mangaorphy/alertreck/docs/figures/chapter5/fig_5_0_training_curves.png

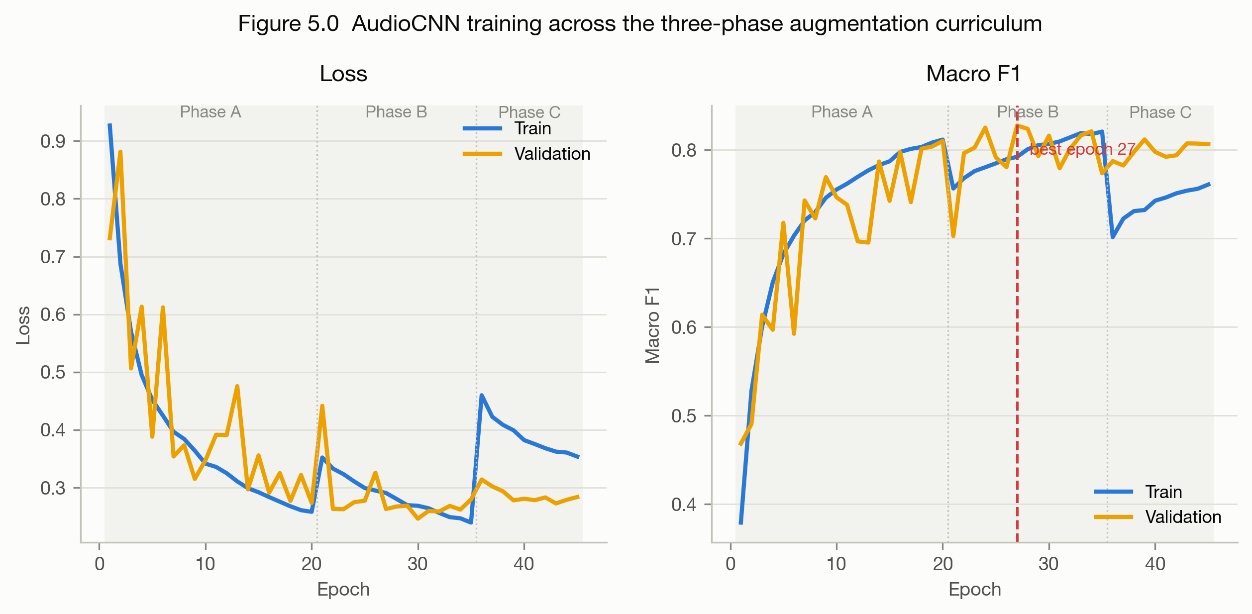
docs/figures/chapter5/fig_5_0_training_curves.png
