mangaorphy/alertreck/docs/figures/chapter5/fig_5_2_per_class_f1.png

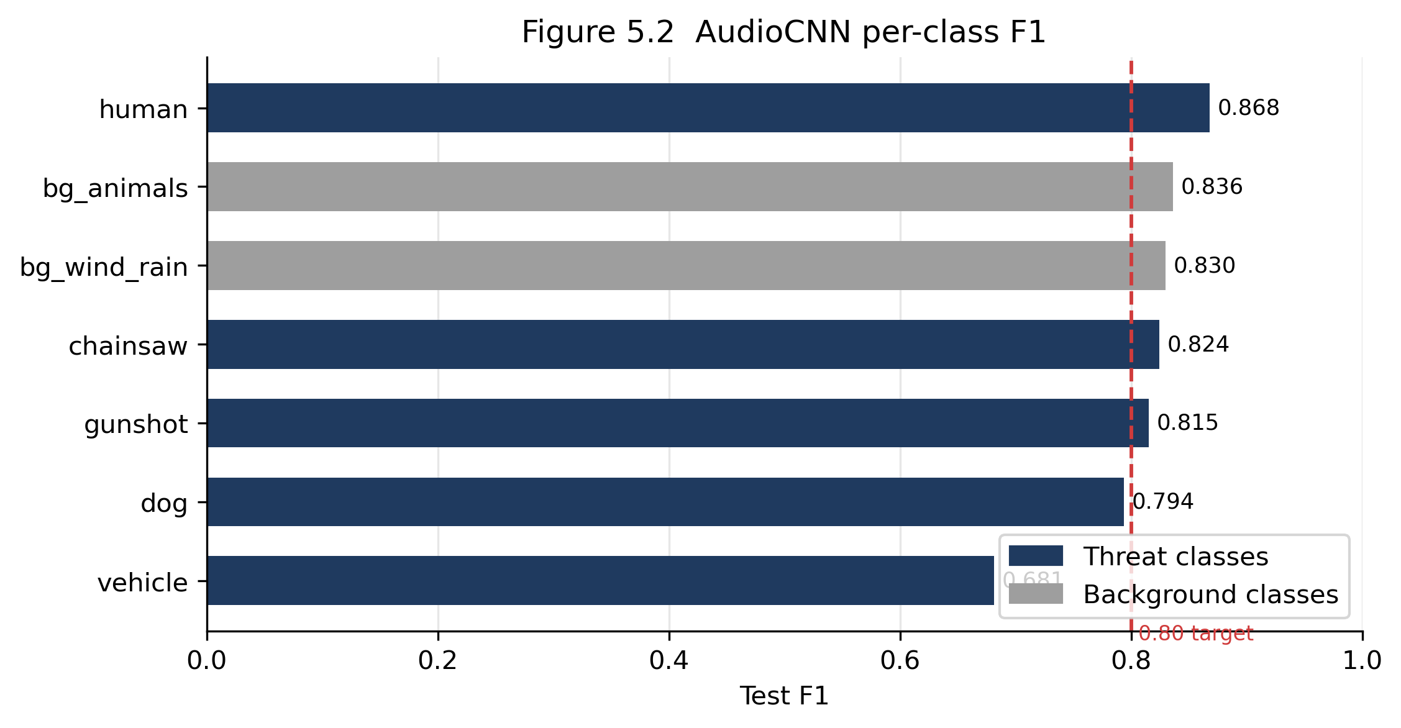
docs/figures/chapter5/fig_5_2_per_class_f1.png
