mangaorphy/alertreck/docs/figures/chapter5/fig_5_3_f1_vs_auc.png

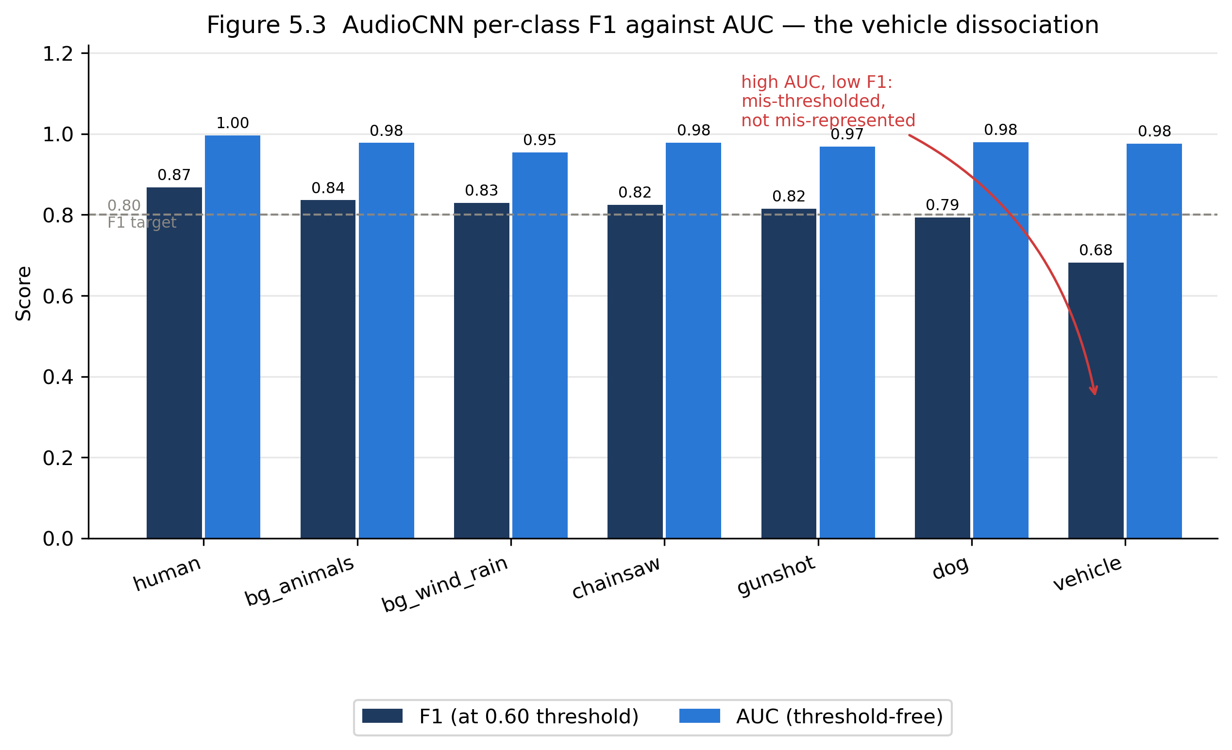
docs/figures/chapter5/fig_5_3_f1_vs_auc.png
