mangaorphy/alertreck/docs/figures/chapter5/fig_5_4_volume_vs_f1.png

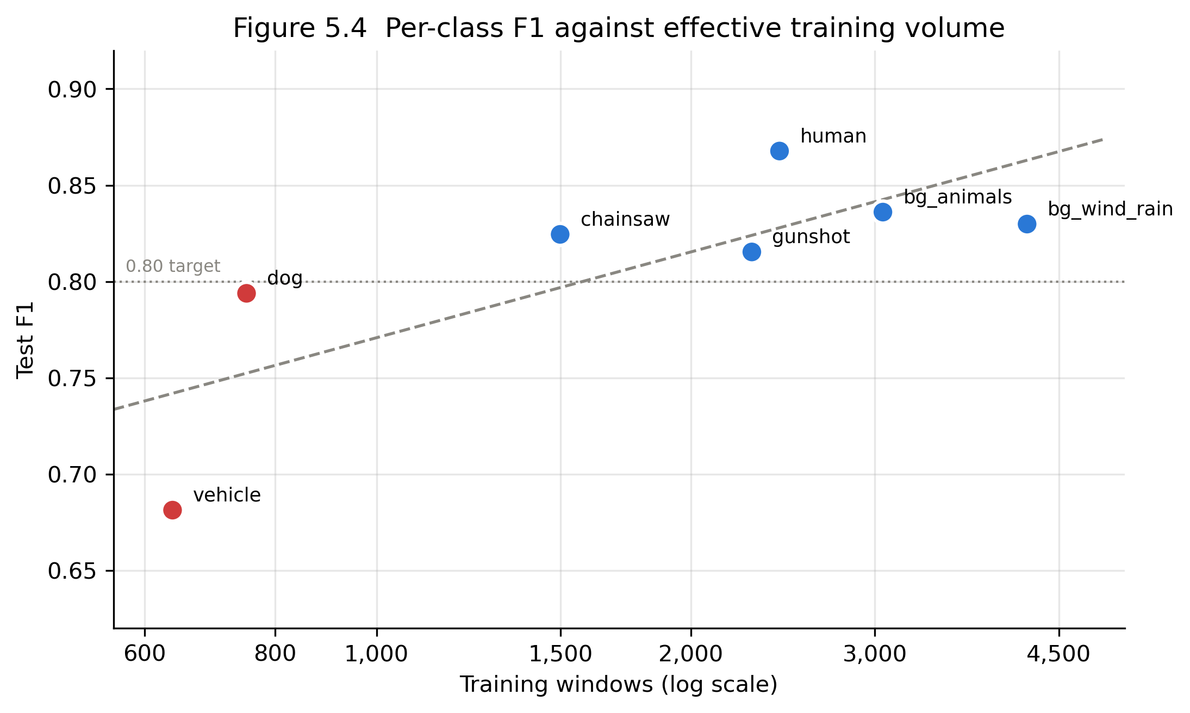
docs/figures/chapter5/fig_5_4_volume_vs_f1.png
