mangaorphy/alertreck/docs/figures/chapter5/fig_5_5_cross_model_f1.png

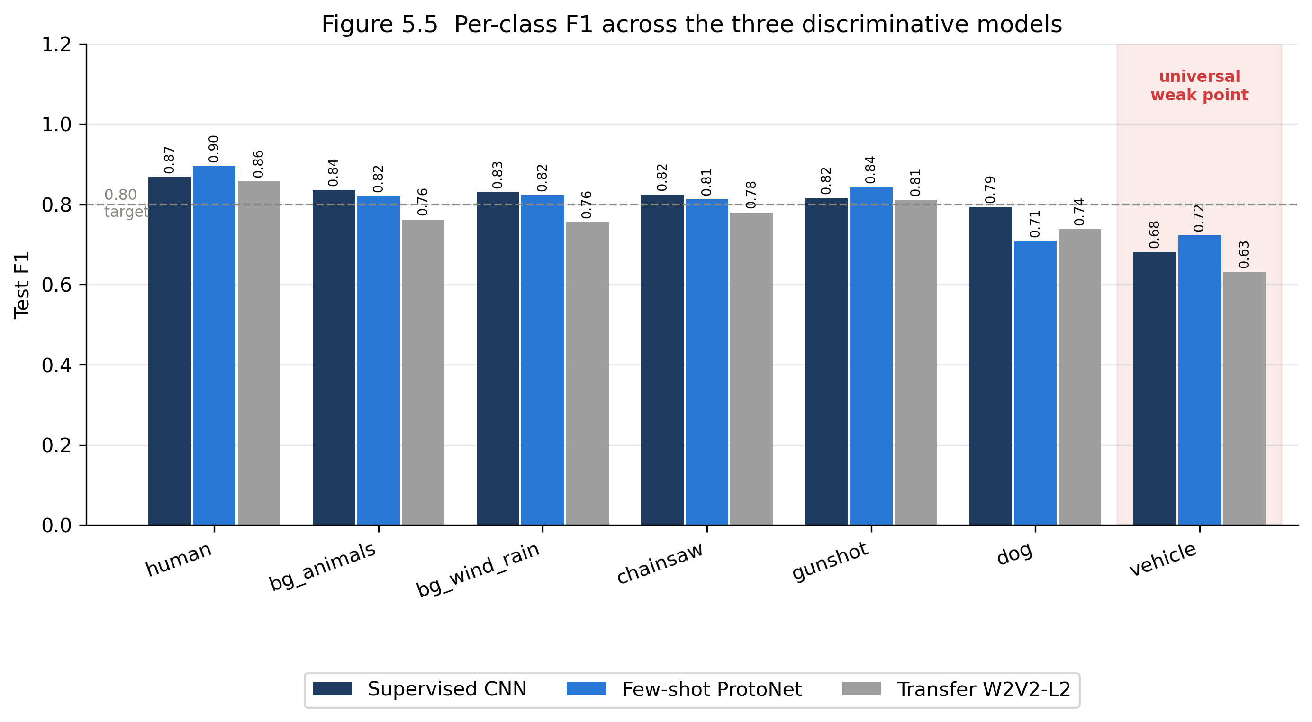
docs/figures/chapter5/fig_5_5_cross_model_f1.png
