mangaorphy/alertreck/docs/figures/chapter5/fig_5_6_anomaly_auc.png

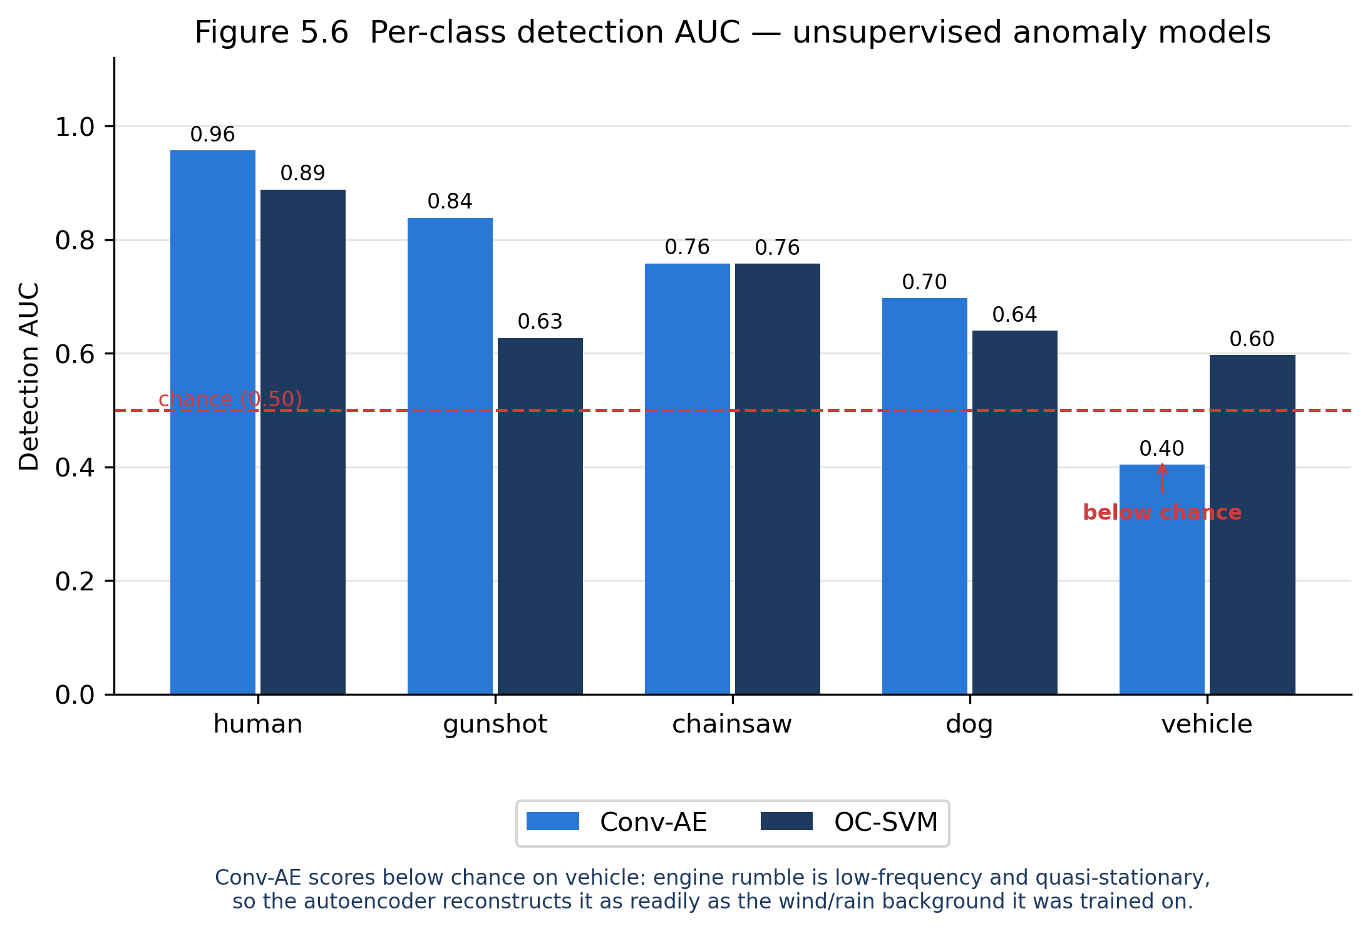
docs/figures/chapter5/fig_5_6_anomaly_auc.png
