mangaorphy/alertreck/docs/figures/chapter5/fig_5_7_confusion_matrix.png

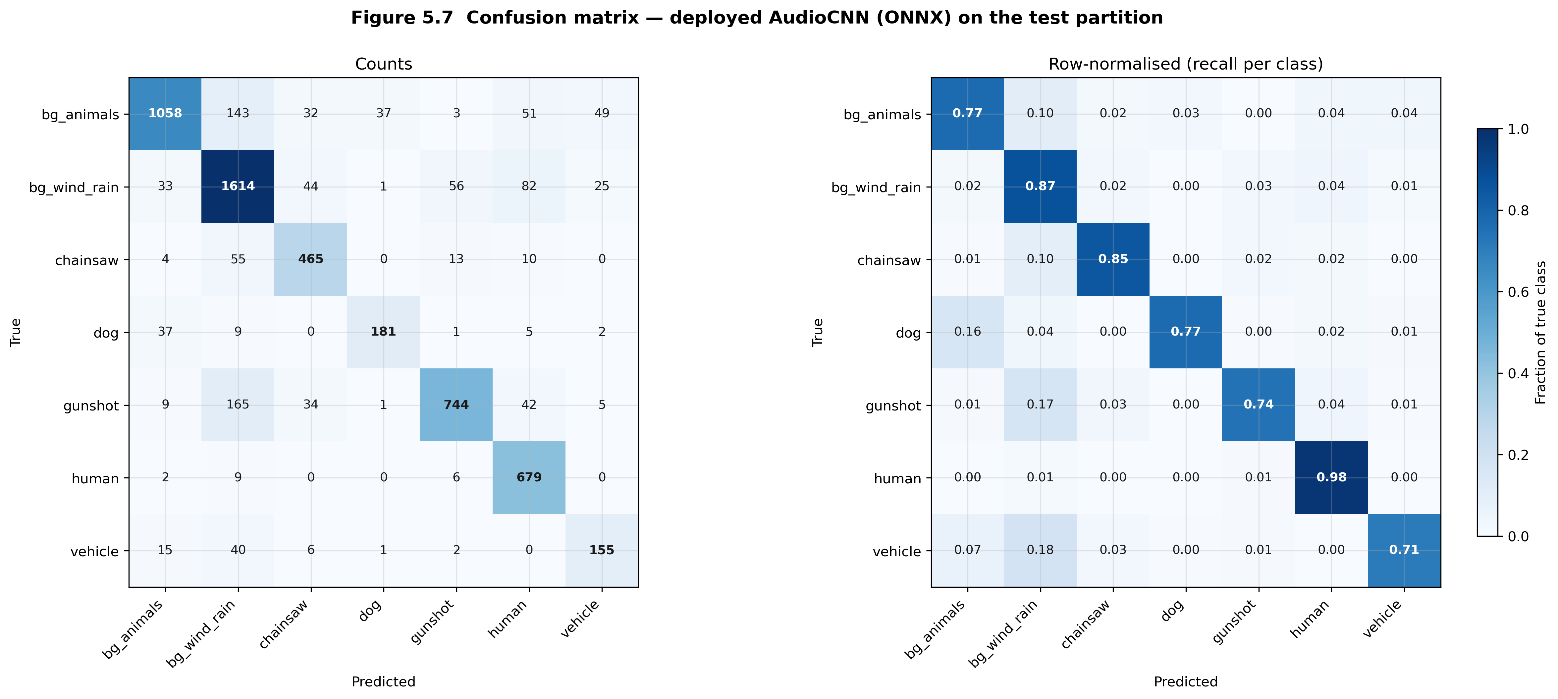
docs/figures/chapter5/fig_5_7_confusion_matrix.png
