mangaorphy/alertreck/docs/figures/feature_samples/0_background_animals.png

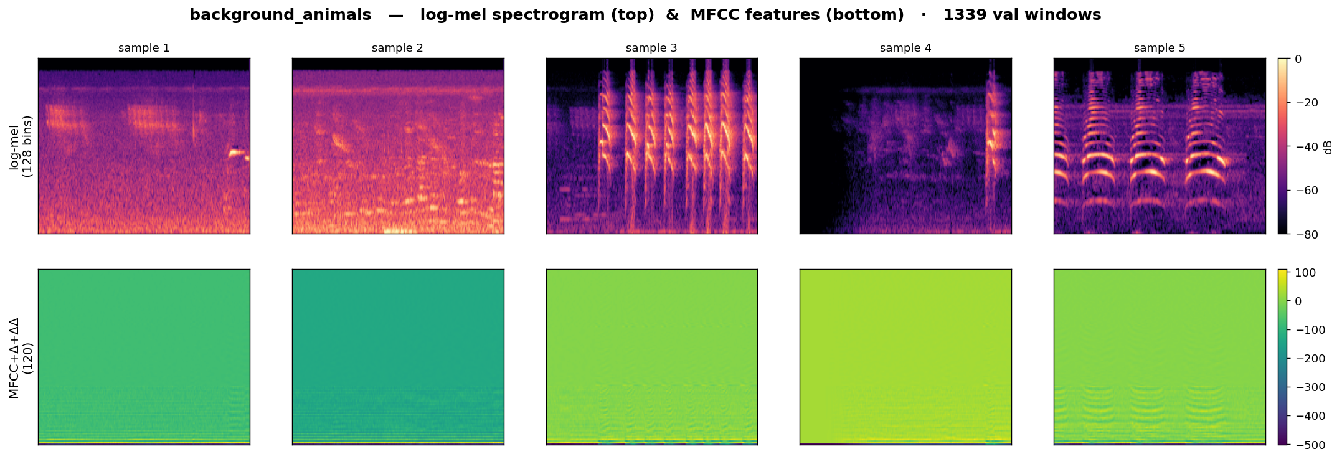
docs/figures/feature_samples/0_background_animals.png
