mangaorphy/alertreck/docs/figures/feature_samples/1_background_wind_rain.png

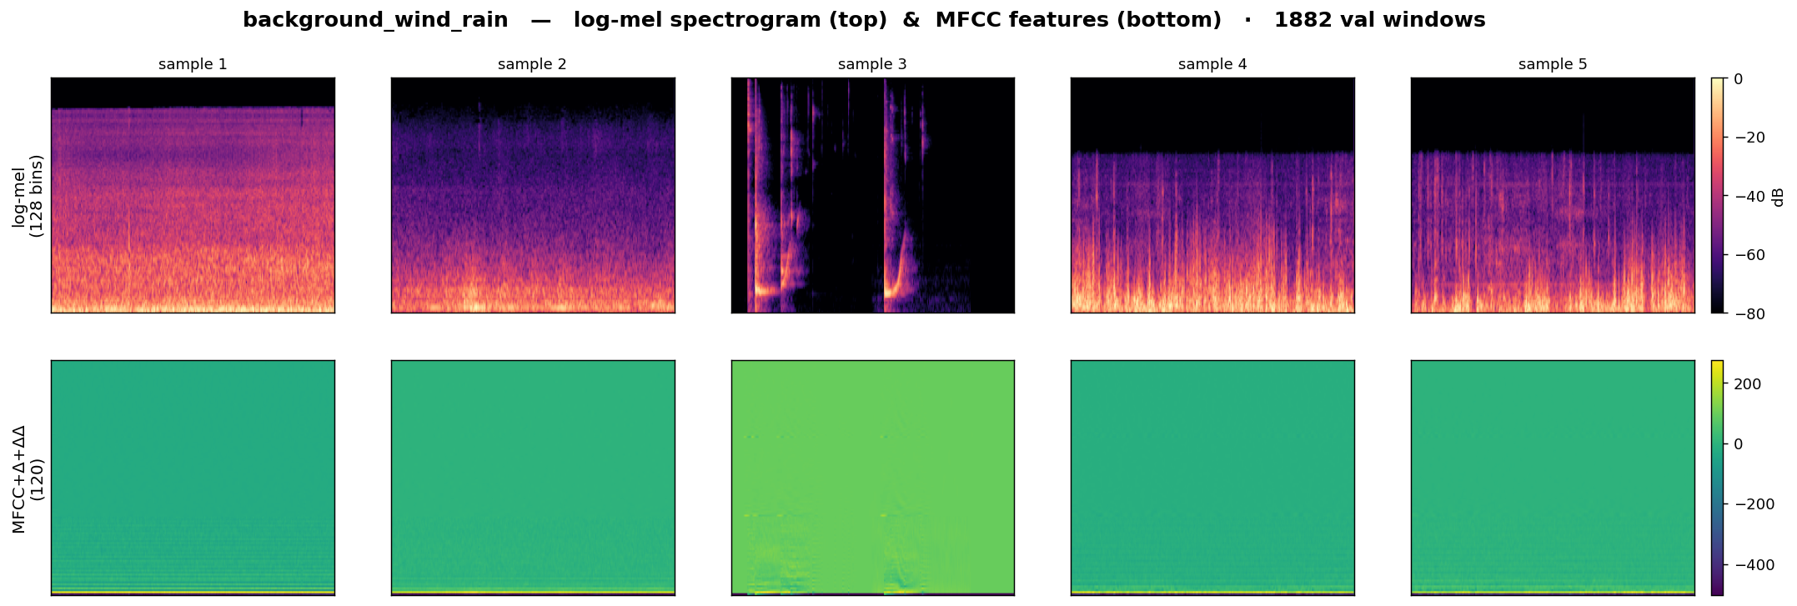
docs/figures/feature_samples/1_background_wind_rain.png
