mangaorphy/alertreck/docs/figures/feature_samples/2_threat_chainsaw.png

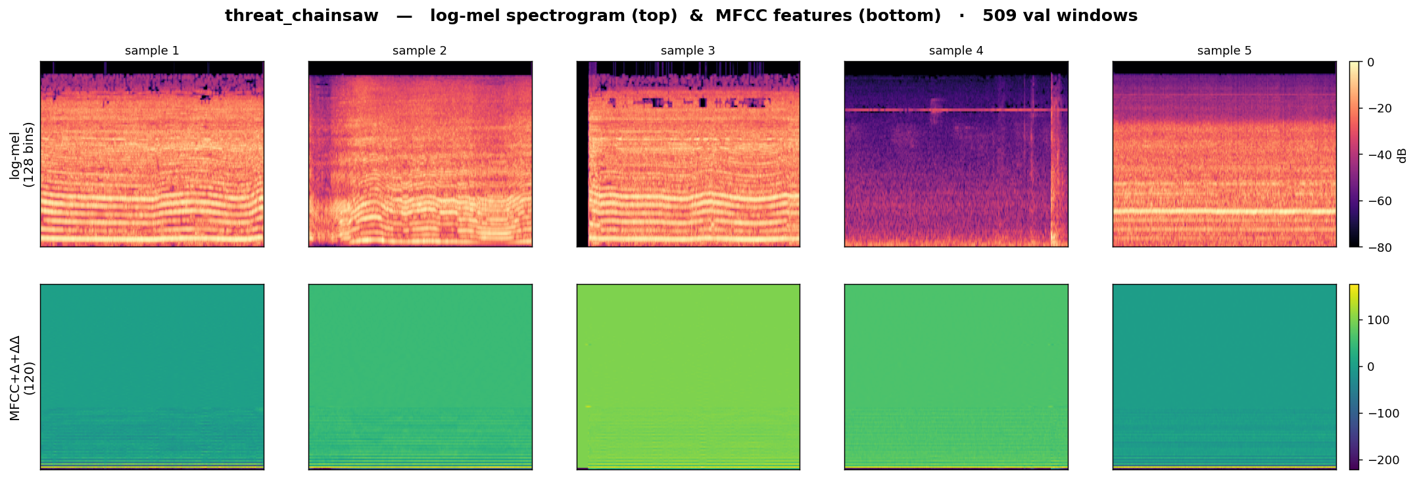
docs/figures/feature_samples/2_threat_chainsaw.png
