mangaorphy/alertreck/docs/figures/feature_samples/4_threat_gunshot.png

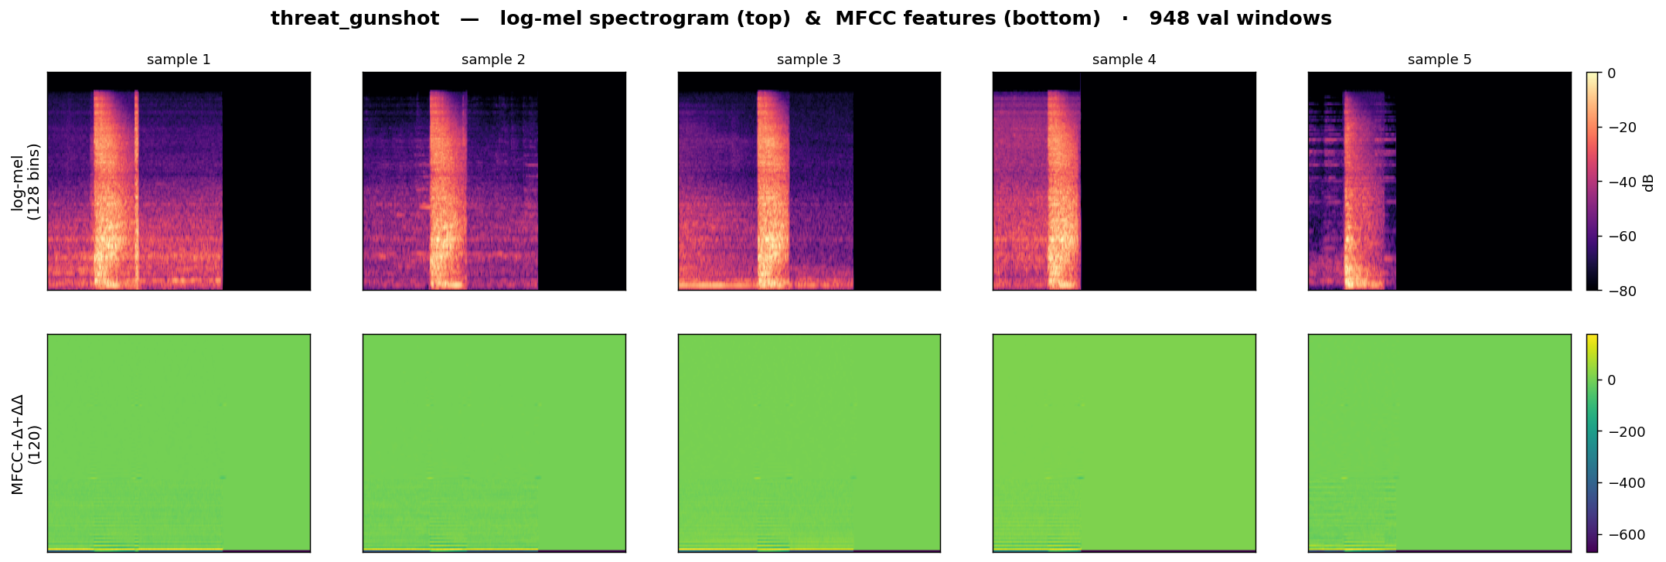
docs/figures/feature_samples/4_threat_gunshot.png
