mangaorphy/alertreck/docs/img/model_output.png

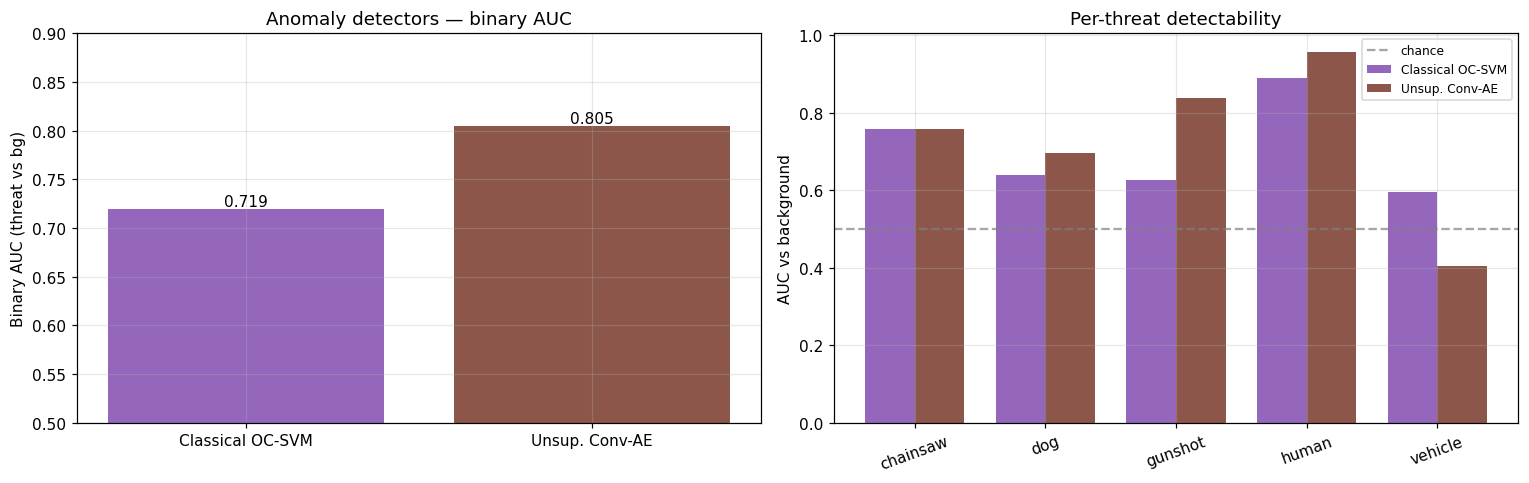
docs/img/model_output.png
